Dengaku/Alphasmart-Neo2-Enclosure/8.jpg

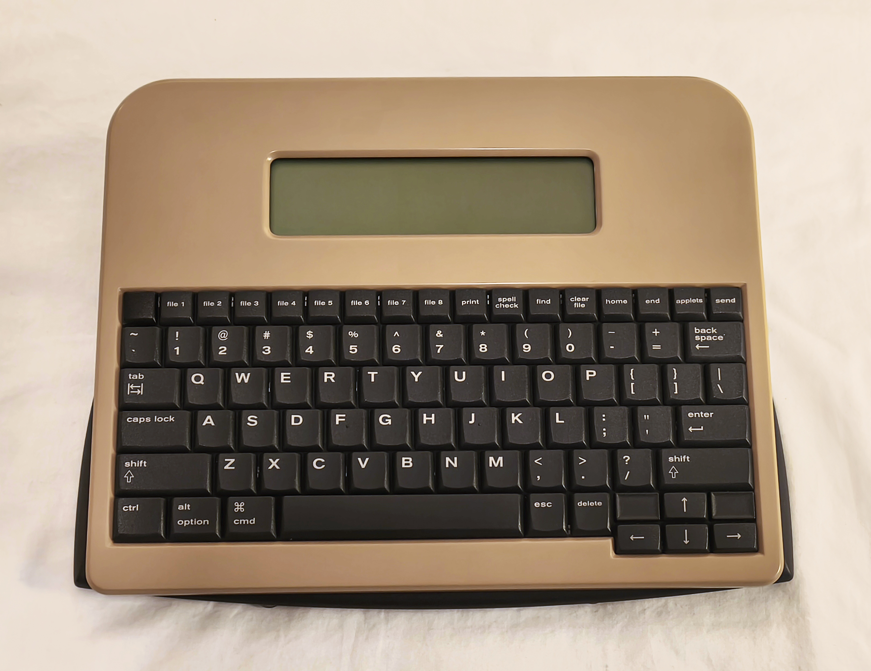
8.jpg
