Dengaku/Alphasmart-Neo2-Enclosure/9.jpg

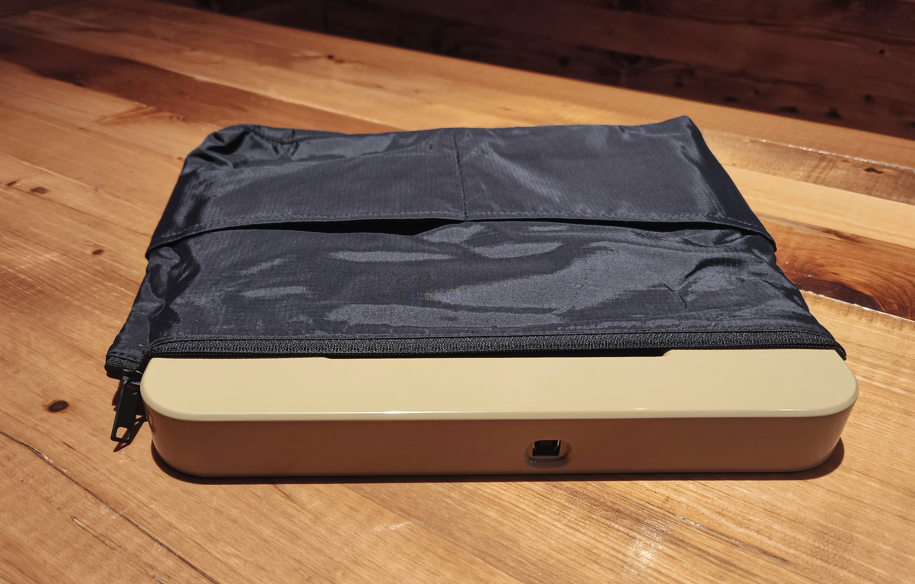
9.jpg
